Pranav-Bonthu/Eclectronics-MiniProject1/ltspice/LTSpiceSchematicMP1.asc

C1: cap; {mc(1u,0.05)}
D1: LED
R1: res; {mc(100k,0.01)}
R2: res; {mc(100k,0.01)}
R3: res; {mc(361.4k,0.01)}
R5: res; {mc(100k,0.01)}
R6: res; {mc(100k,0.01)}
RLED: res; 269.8
U1: opamprails
U2: opamprails
VDD: voltage; 3.3V
Named nets: 0, Vout, VDD, CRNet
.tran 0 5 0
.meas TRAN Tperiod TRIG V(vout)=1.65 RISE=2 TARG V(vout)=1.65 RISE=3
.ic V(CRNet)=0
.step param run 1 200 1
